klushok-etv/christmas2021/pcb/svg_export/.svg2shenzhen-cache/images/Dwgs.User_g838.png

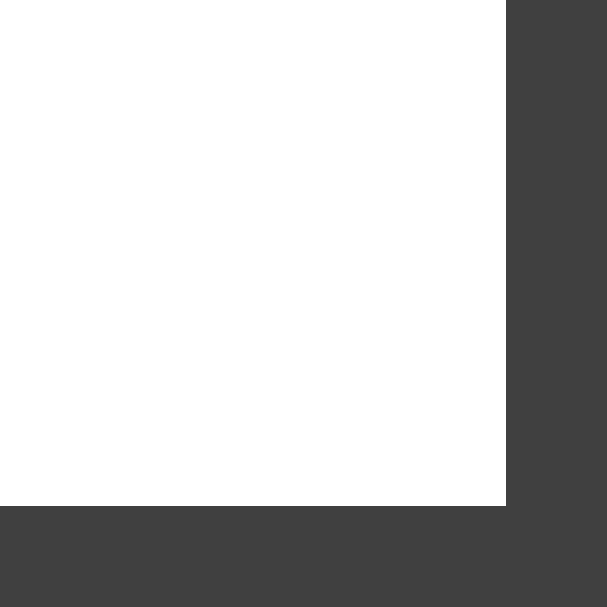
pcb/svg_export/.svg2shenzhen-cache/images/Dwgs.User_g838.png
