klushok-etv/christmas2021/pcb/svg_export/.svg2shenzhen-cache/images/F.SilkS_g836.png

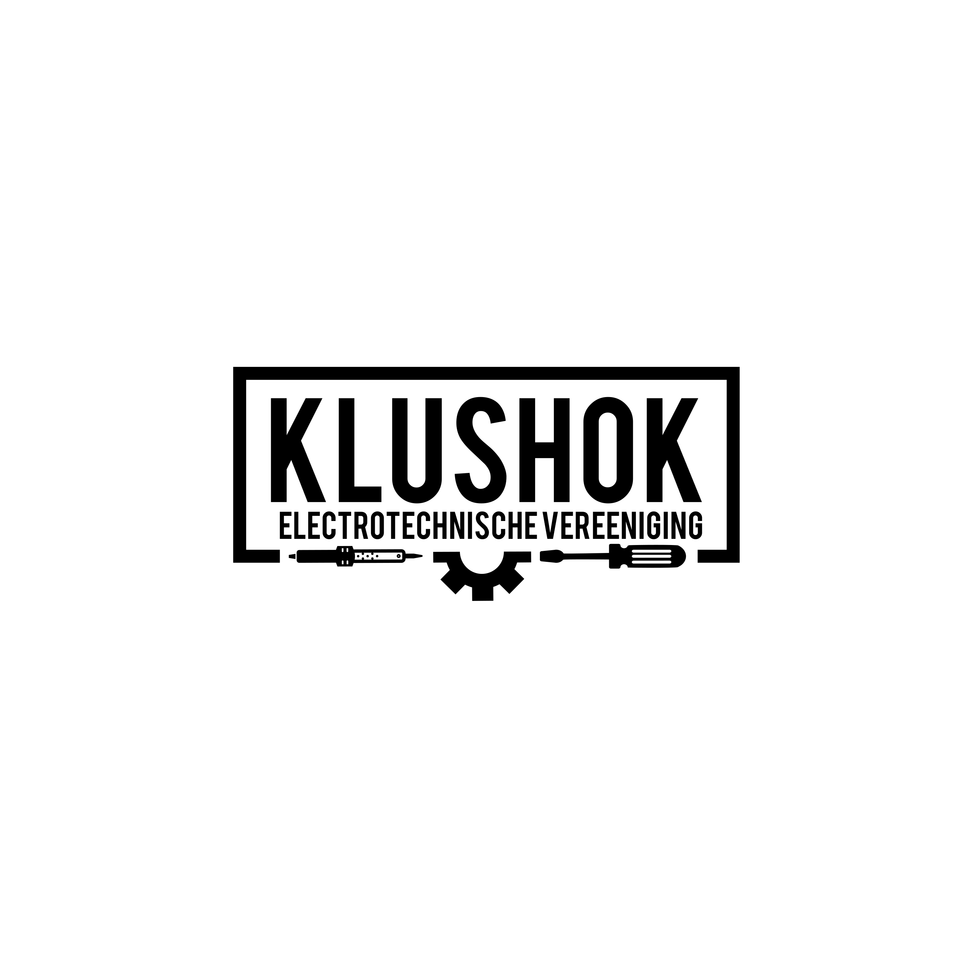
pcb/svg_export/.svg2shenzhen-cache/images/F.SilkS_g836.png
