klushok-etv/christmas2021/pcb/svg_export_prog_module/.svg2shenzhen-cache/images/Dwgs.User_g2293.png

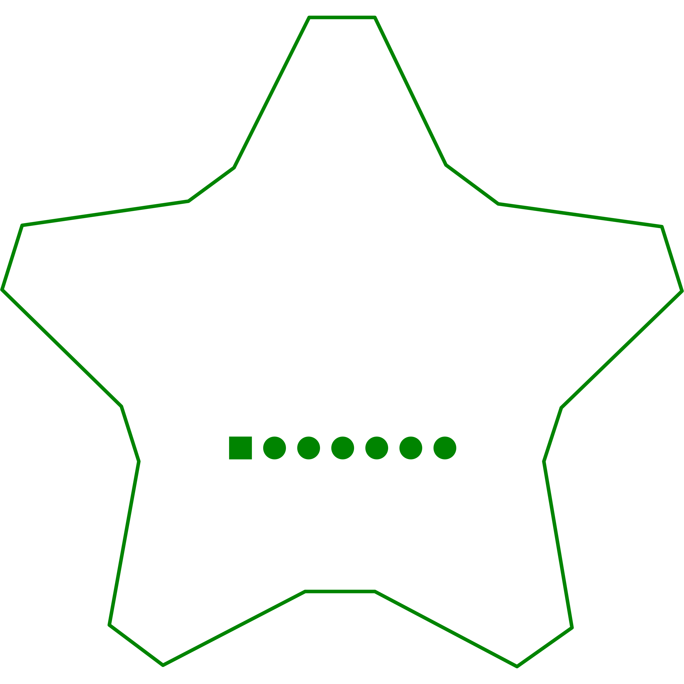
pcb/svg_export_prog_module/.svg2shenzhen-cache/images/Dwgs.User_g2293.png
