klushok-etv/christmas2021/images/manual/cap-elec.png

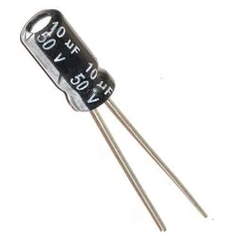
images/manual/cap-elec.png
