klushok-etv/christmas2021/images/manual/SOT-23-5.jpg

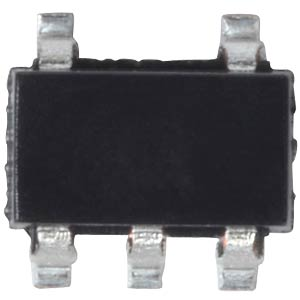
images/manual/SOT-23-5.jpg
