klushok-etv/christmas2021/images/manual/wires.png

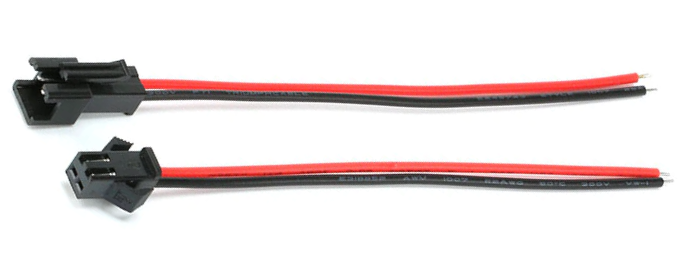
images/manual/wires.png
